svenpetersen1965/C64-CHARSET-Adaptor-Switch/Rev. 1/pictures/IMG_2266.JPG

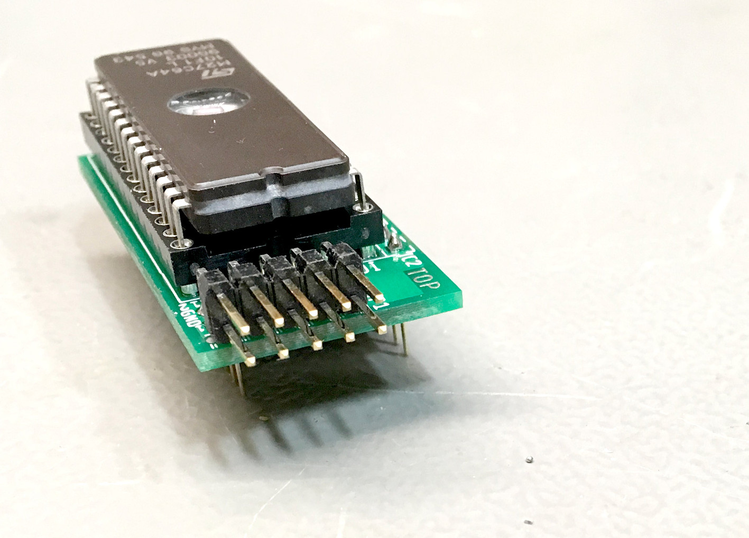
Rev. 1/pictures/IMG_2266.JPG
